KoljaWindeler/ESP8266_mqtt_pwm_pir_temp/JKW_MQTT_PWM_PIR_TEMP/src/src/capability.h

#ifndef capability_h
#define capability_h

//#include <Arduino.h>
#include "main.h"

class capability {
	public:
		capability();
		bool parse_eeprom(uint8_t* e);
		bool parse(unsigned char* input, uint8_t* key, uint8_t* dep);
		bool parse(unsigned char* input, uint8_t* key);
		bool ensure_dep(unsigned char* input, uint8_t* dep);
};

extern capability cap;

#endif
